KeatonMasuda/ak280-schematics/hardware/AK-280.kicad_sch

## KiCad design hardware/AK-280.kicad_sch (2026-06-29)

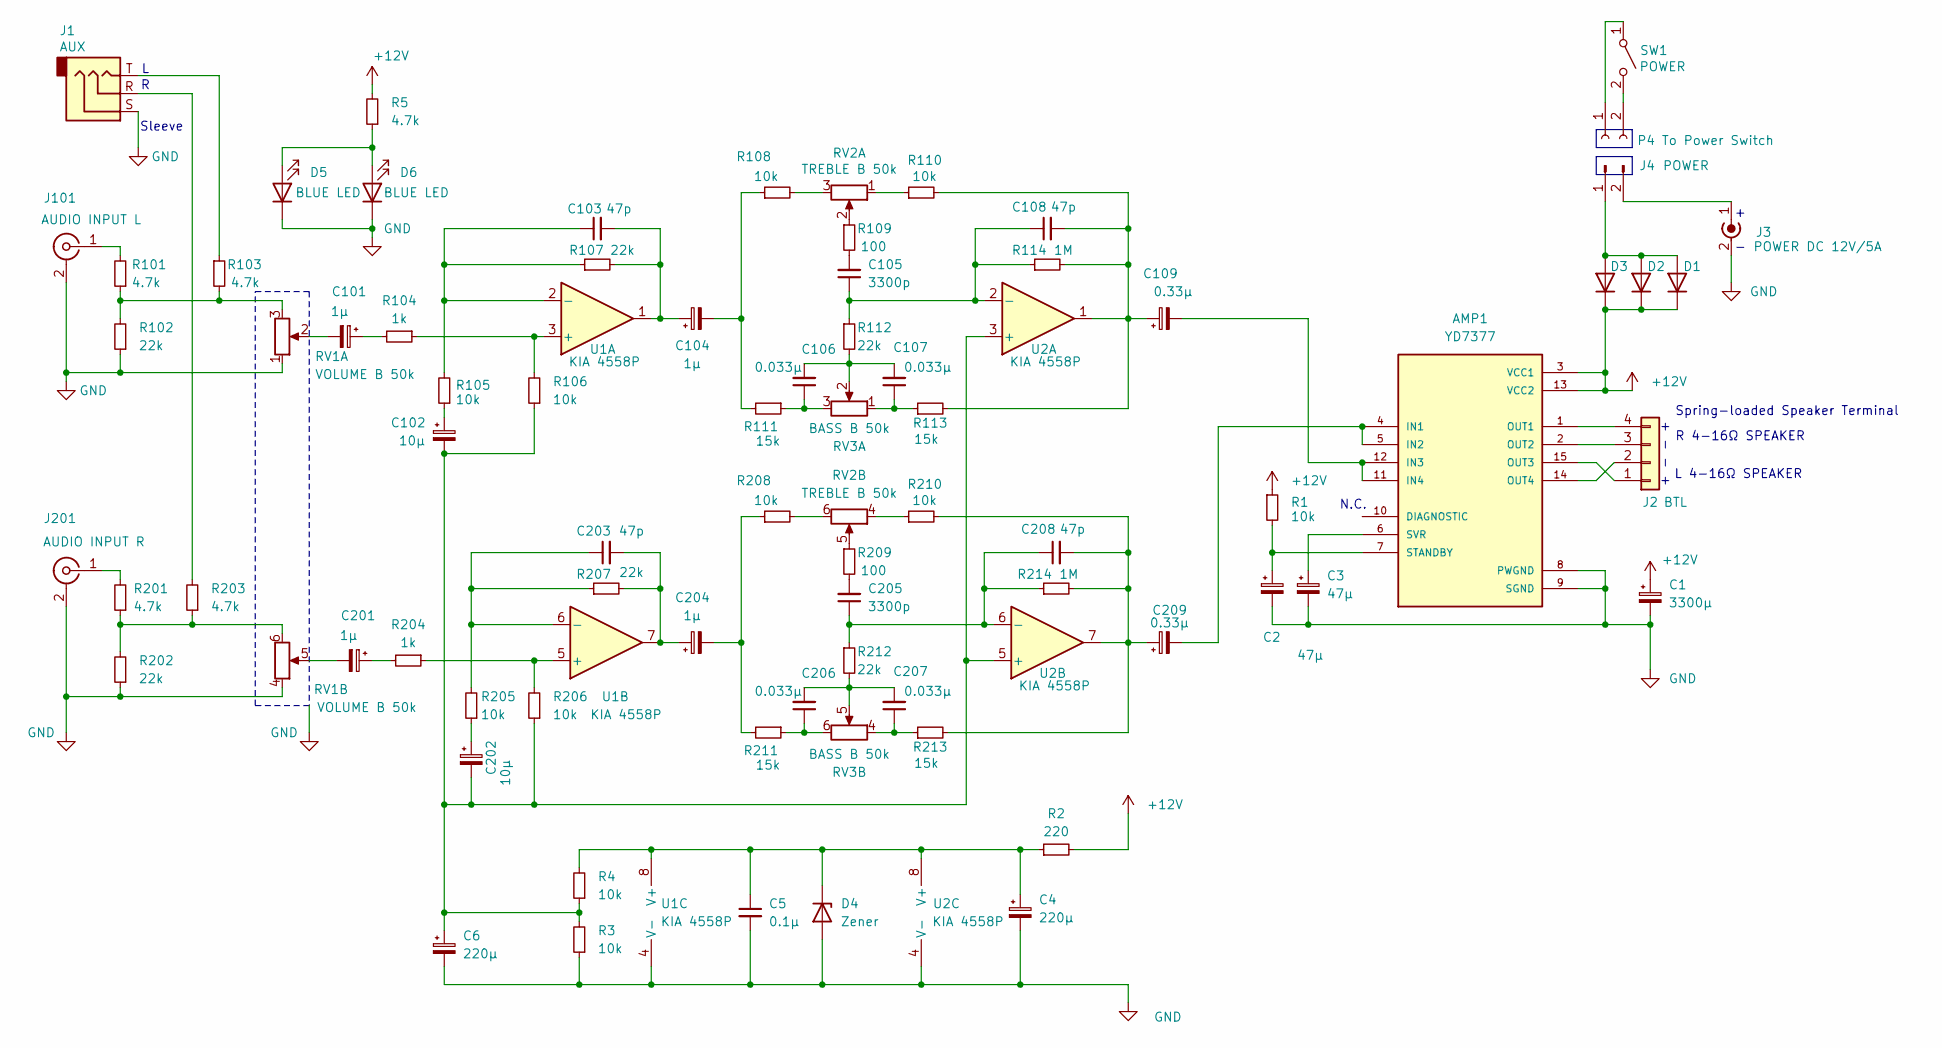
[picture p4: schematic AK-280.kicad_sch]

Parts:
AMP1: YD7377; AMP_TDA7377
C1: 3300μ; Voltage 16V
C2, C3: 47μ; Voltage 25V
C4, C6: 220μ; Voltage 16V
C5: 0.1μ
C101, C104, C201, C204: 1μ; Voltage 50V
C102, C202: 10μ; Voltage 50V
C103, C108, C203, C208: 47p
C105, C205: 3300p
C106, C107, C206, C207: 0.033μ
C109, C209: 0.33μ; Voltage 50V
D1, D2, D3: 1N5400; D_DO-201AD_P15.24mm_Horizontal
D4: Zener; Voltage 9.1V
D5, D6: BLUE LED
J1: AUX
J2: BTL
J3: POWER DC 12V/5A
J4: POWER
J101: AUDIO INPUT L
J201: AUDIO INPUT R
P4: To Power Switch
R1, R3, R4, R105, R106, R108, R110, R205, R206, R208, R210: 10k
R2: 220
R5, R101, R103, R201, R203: 4.7k
R102, R107, R112, R202, R207, R212: 22k
R104, R204: 1k
R109, R209: 100
R111, R113, R211, R213: 15k
R114, R214: 1M
RV1: VOLUME B 50k
RV2: TREBLE B 50k
RV3: BASS B 50k
SW1: POWER
U1, U2: KIA 4558P

Connections:
+12V: AMP1.3 (VCC1), AMP1.13 (VCC2), C1.1, D1.1 (K), D2.1 (K), D3.1 (K), R1.1, R2.2, R5.2
GND: AMP1.8 (PWGND), AMP1.9 (SGND), C1.2, C2.2, C3.2, C4.2, C5.2, C6.2, D4.2 (A), D5.1 (K), D6.1 (K), J1.S, J3.2 (Ext), J101.2 (Ext), J201.2 (Ext), R3.1, R102.1, R202.1, RV1.1, RV1.4, U1.4 (V-), U2.4 (V-)
unnamed: AMP1.1 (OUT1), J2.4
unnamed: AMP1.2 (OUT2), J2.3
unnamed: AMP1.4 (IN1), AMP1.5 (IN2), C209.2
unnamed: AMP1.6 (SVR), C3.1
unnamed: AMP1.7 (STANDBY), C2.1, R1.2
unnamed: AMP1.11 (IN4), AMP1.12 (IN3), C109.2
unnamed: AMP1.14 (OUT4), J2.2
unnamed: AMP1.15 (OUT3), J2.1
unnamed: C4.1, C5.1, D4.1 (K), R2.1, R4.2, U1.8 (V+), U2.8 (V+)
unnamed: C101.1, R104.2
unnamed: C101.2, RV1.2
unnamed: C102.1, R105.1
unnamed: C6.1, C102.2, C202.2, R3.2, R4.1, R106.1, R206.1, U2.3 (+), U2.5 (+)
unnamed: C103.1, R105.2, R107.1, U1.2 (-)
unnamed: C103.2, C104.1, R107.2, U1.1
unnamed: C104.2, R108.1, R111.2
unnamed: C105.1, C108.1, R112.1, R114.1, U2.2 (-)
unnamed: C105.2, R109.2
unnamed: C106.1, R111.1, RV3.3
unnamed: C106.2, C107.2, R112.2, RV3.2
unnamed: C107.1, R113.1, RV3.1
unnamed: C108.2, C109.1, R110.2, R113.2, R114.2, U2.1
unnamed: C201.1, R204.2
unnamed: C201.2, RV1.5
unnamed: C202.1, R205.1
unnamed: C203.1, R205.2, R207.1, U1.6 (-)
unnamed: C203.2, C204.1, R207.2, U1.7
unnamed: C204.2, R208.1, R211.2
unnamed: C205.1, C208.1, R212.1, R214.1, U2.6 (-)
unnamed: C205.2, R209.2
unnamed: C206.1, R211.1, RV3.6
unnamed: C206.2, C207.2, R212.2, RV3.5
unnamed: C207.1, R213.1, RV3.4
unnamed: C208.2, C209.1, R210.2, R213.2, R214.2, U2.7
unnamed: D1.2 (A), D2.2 (A), D3.2 (A), J4.1
unnamed: D5.2 (A), D6.2 (A), R5.1
unnamed: J1.R, R203.2
unnamed: J1.T, R103.1
unnamed: J3.1 (In), J4.2
unnamed: J101.1 (In), R101.2
unnamed: J201.1 (In), R201.2
unnamed: P4.1, SW1.1 (A)
unnamed: P4.2, SW1.2 (B)
unnamed: R101.1, R102.2, R103.2, RV1.3
unnamed: R104.1, R106.2, U1.3 (+)
unnamed: R108.2, RV2.3
unnamed: R109.1, RV2.2
unnamed: R110.1, RV2.1
unnamed: R201.1, R202.2, R203.1, RV1.6
unnamed: R204.1, R206.2, U1.5 (+)
unnamed: R208.2, RV2.6
unnamed: R209.1, RV2.5
unnamed: R210.1, RV2.4

Notes on the sheet:
N.C.
Spring-loaded Speaker Terminal
L 4-16Ω SPEAKER
R 4-16Ω SPEAKER
Sleeve
